HW-Lab-Hardware-Design-Agency/WebScreen-PCB/kicad_project/3Dlib/MicroSD_Socket.STEP

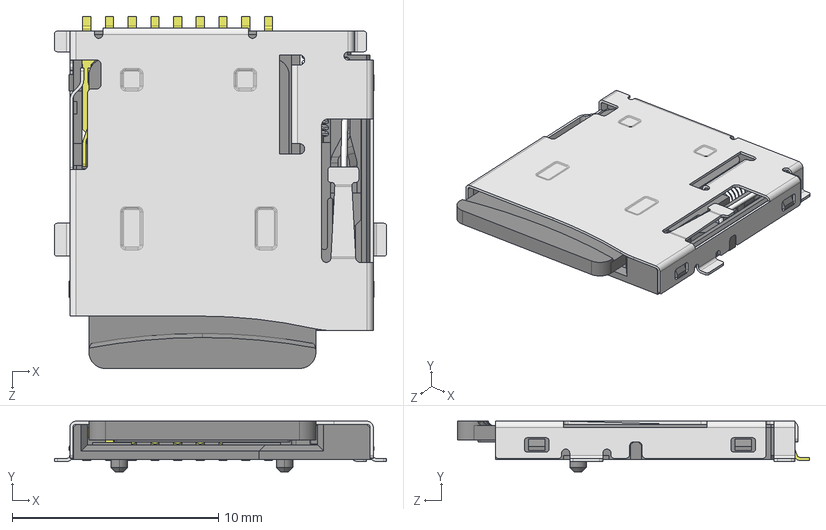
[picture p17: CAD file, 2024-11-25]
kicad_project/3Dlib/MicroSD_Socket.STEP
16.1 x 2.45 x 17.0 mm
Case^MicroSD_Socket
Insert^MicroSD_Socket
Brace^MicroSD_Socket
Spring^MicroSD_Socket
Lid^MicroSD_Socket
Pin_Middle^MicroSD_Socket x 5
Pin_Short^MicroSD_Socket
Pin_Long^MicroSD_Socket x 2
MicroSD_Card^MicroSD_Socket
Pin_CardIn^MicroSD_Socket
