HW-Lab-Hardware-Design-Agency/WebScreen-PCB/kicad_project/3Dlib/33FXRH-SM1-GAN-TF.STEP

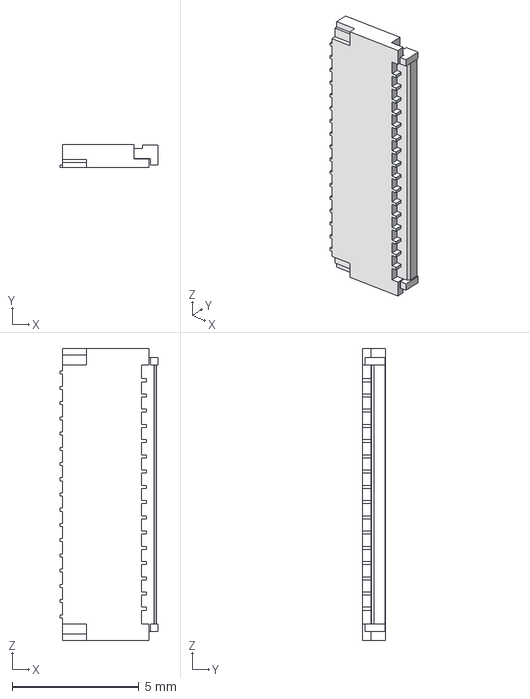
[picture p18: CAD file, 2024-11-25]
kicad_project/3Dlib/33FXRH-SM1-GAN-TF.STEP
3.85 x 0.9 x 11.5 mm
