HW-Lab-Hardware-Design-Agency/WebScreen-PCB/kicad_project/3Dlib/L_0201_0603Metric.step

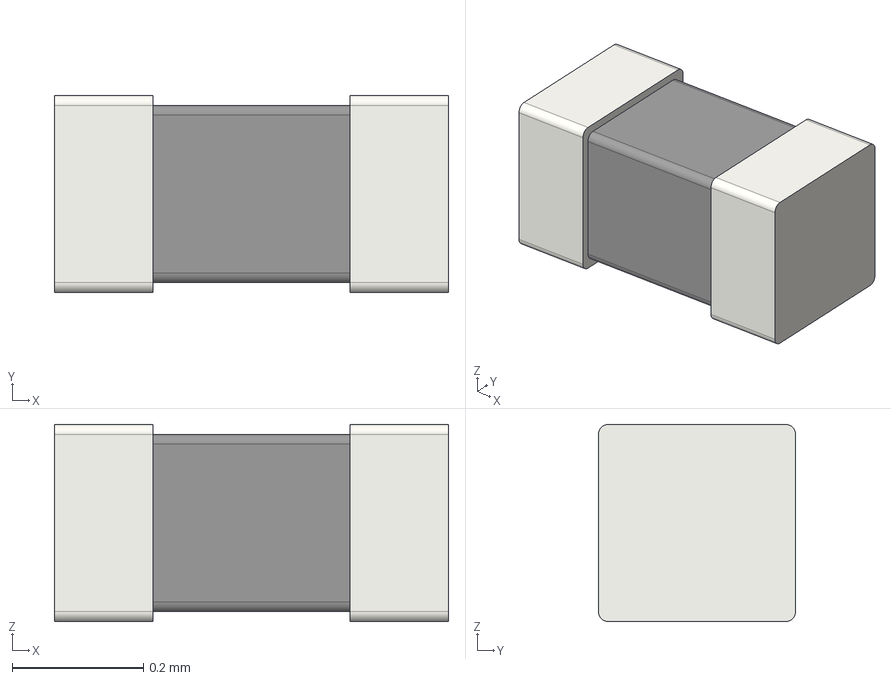
[picture p19: CAD file, 2024-11-25]
kicad_project/3Dlib/L_0201_0603Metric.step
0.6 x 0.3 x 0.3 mm
