HW-Lab-Hardware-Design-Agency/WebScreen-PCB/kicad_project/3Dlib/USB_C_HC019-1E1H1A103-0HR.step

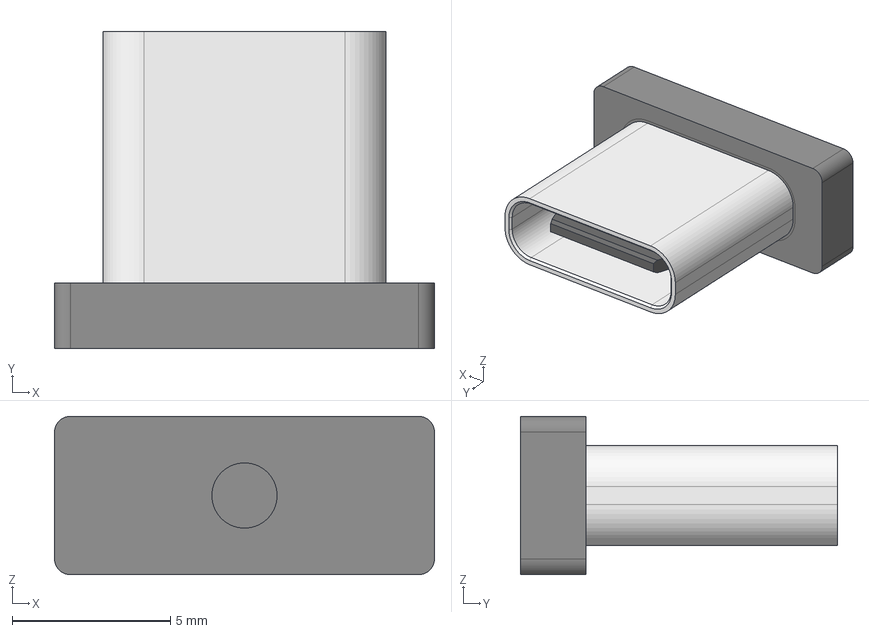
[picture p20: CAD file, 2024-11-25]
kicad_project/3Dlib/USB_C_HC019-1E1H1A103-0HR.step
12.0 x 10.0 x 5.00 mm
