HW-Lab-Hardware-Design-Agency/WebScreen-PCB/kicad_project/3Dlib/r_0402_h040.step

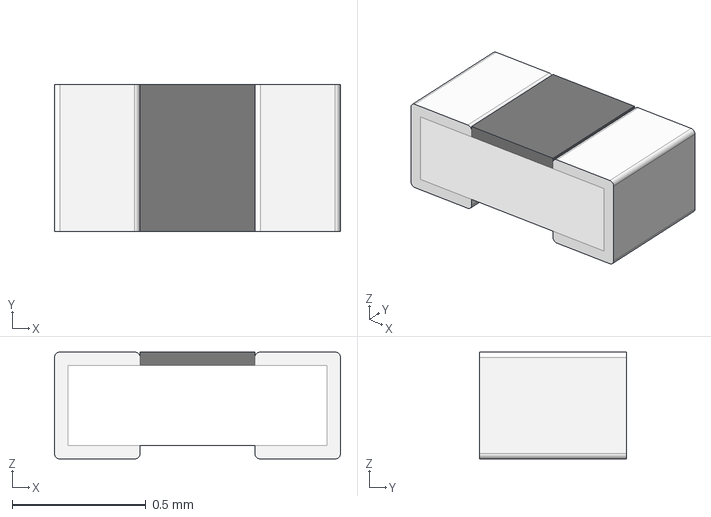
[picture p21: CAD file, 2024-11-25]
kicad_project/3Dlib/r_0402_h040.step
1.07 x 0.55 x 0.4 mm
