HW-Lab-Hardware-Design-Agency/WebScreen-PCB/kicad_project/3Dlib/c_1206_h160.step

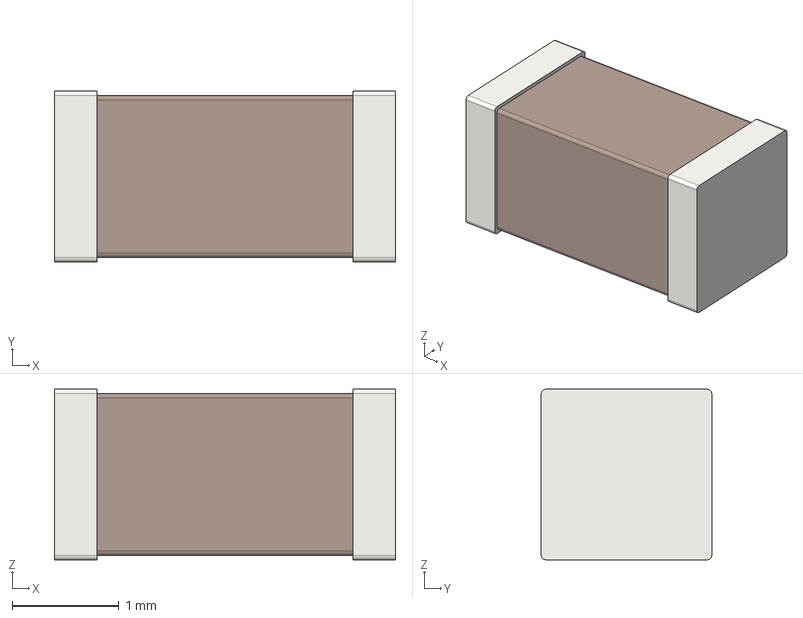
[picture p22: CAD file, 2024-11-25]
kicad_project/3Dlib/c_1206_h160.step
3.20 x 1.60 x 1.60 mm
