HW-Lab-Hardware-Design-Agency/WebScreen-PCB/kicad_project/3Dlib/AXPM65611.step

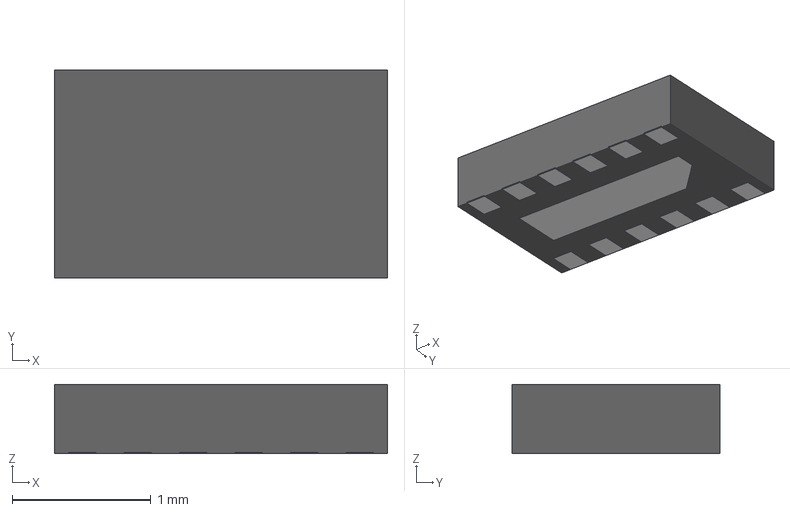
[picture p23: CAD file, 2024-11-25]
kicad_project/3Dlib/AXPM65611.step
2.40 x 1.50 x 0.5 mm
main_Body001
mainPad001
