HW-Lab-Hardware-Design-Agency/WebScreen-PCB/kicad_project/3Dlib/c_1210.step

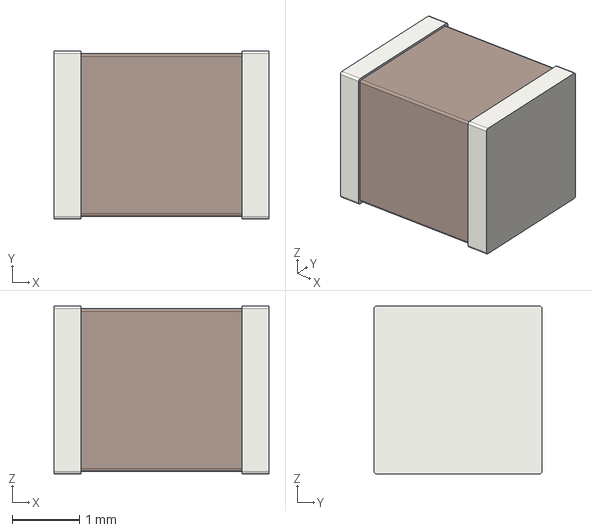
[picture p24: CAD file, 2024-11-25]
kicad_project/3Dlib/c_1210.step
3.20 x 2.50 x 2.50 mm
