HW-Lab-Hardware-Design-Agency/WebScreen-PCB/kicad_project/3Dlib/SY8089A1AAC.stp

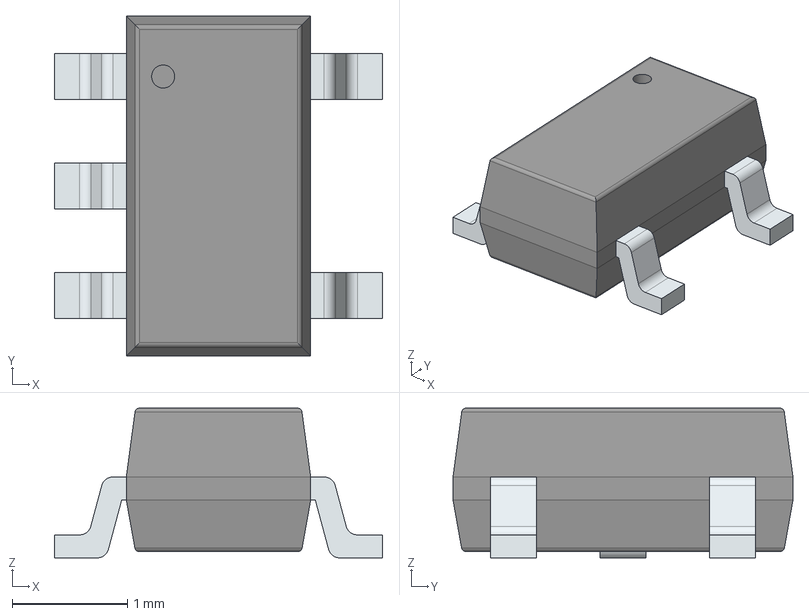
[picture p25: CAD file, 2024-11-25]
kicad_project/3Dlib/SY8089A1AAC.stp
2.85 x 2.95 x 1.30 mm
PinsArrayL
PinsArrayR
