HW-Lab-Hardware-Design-Agency/WebScreen-PCB/kicad_project/3Dlib/C_0402_1005Metric.step

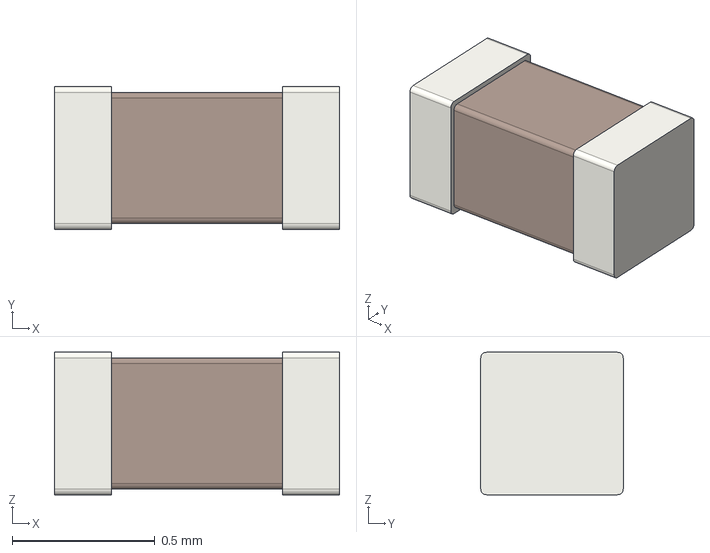
[picture p26: CAD file, 2024-11-25]
kicad_project/3Dlib/C_0402_1005Metric.step
1.00 x 0.5 x 0.5 mm
