HW-Lab-Hardware-Design-Agency/WebScreen-PCB/kicad_project/3Dlib/BRFL2518T1R0M.STEP

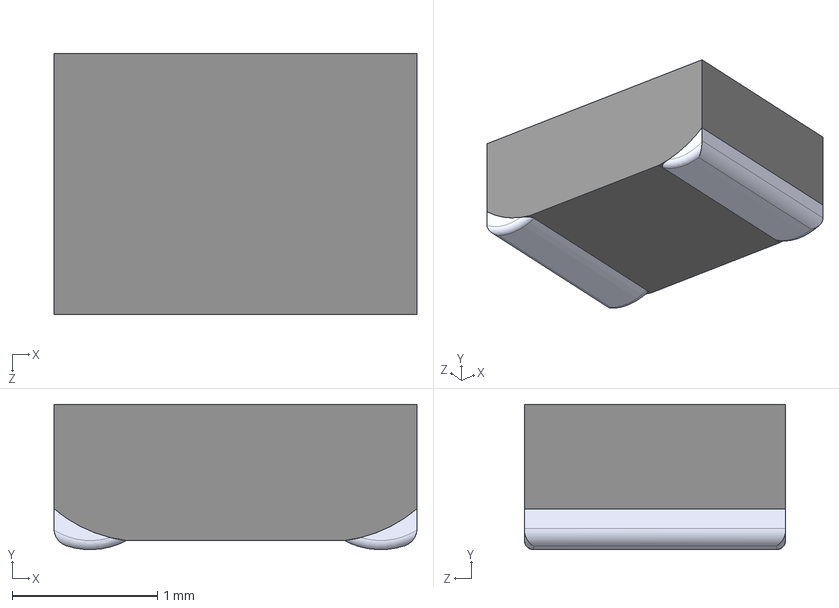
[picture p27: CAD file, 2024-11-25]
kicad_project/3Dlib/BRFL2518T1R0M.STEP
2.50 x 1 x 1.80 mm
