HW-Lab-Hardware-Design-Agency/WebScreen-PCB/kicad_project/3Dlib/led_0603.step

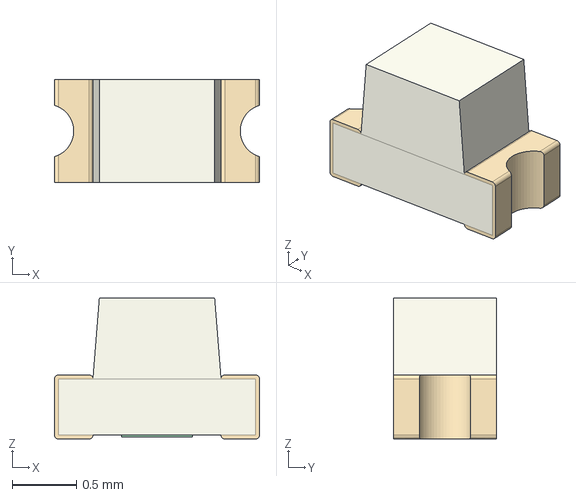
[picture p28: CAD file, 2024-11-25]
kicad_project/3Dlib/led_0603.step
1.60 x 0.8 x 1.10 mm
