HW-Lab-Hardware-Design-Agency/WebScreen-PCB/kicad_project/3Dlib/Crystal_SMD_3225-4Pin_3.2x2.5mm.step

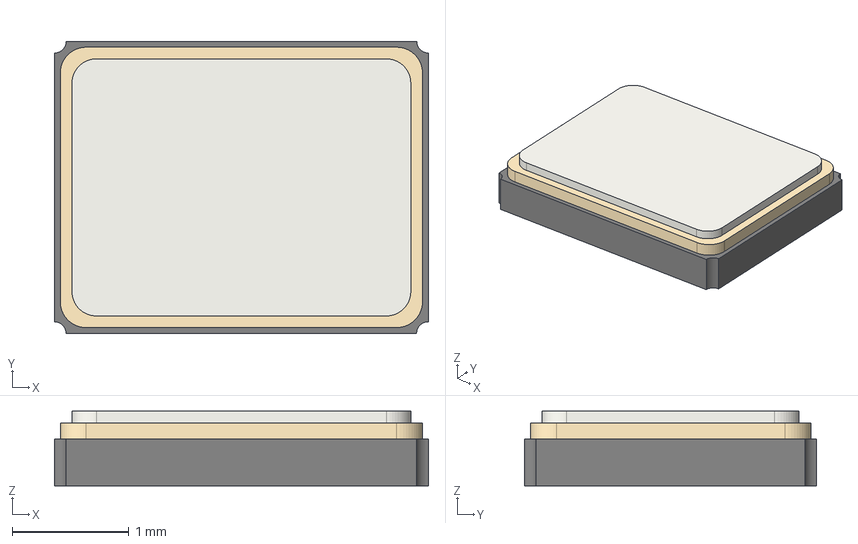
[picture p29: CAD file, 2024-11-25]
kicad_project/3Dlib/Crystal_SMD_3225-4Pin_3.2x2.5mm.step
3.20 x 2.50 x 0.64 mm
