HW-Lab-Hardware-Design-Agency/WebScreen-PCB/kicad_project/3Dlib/ESP32-S3R8.stp

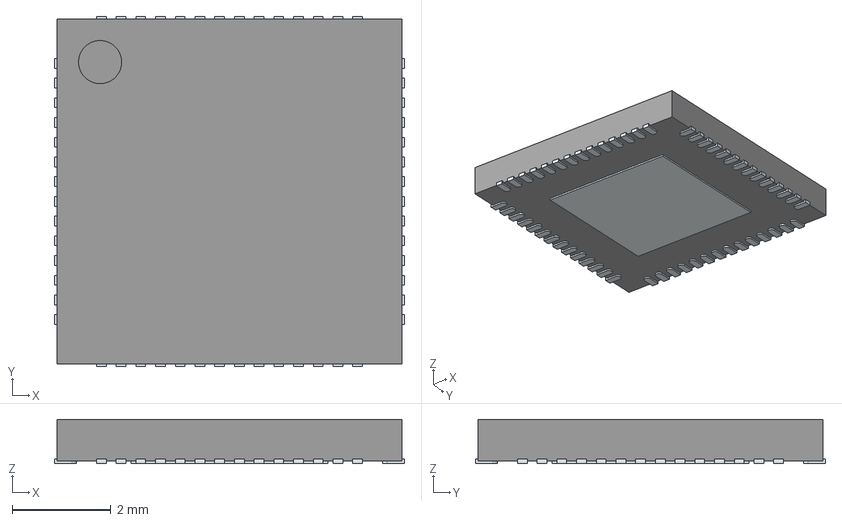
[picture p30: CAD file, 2024-11-25]
kicad_project/3Dlib/ESP32-S3R8.stp
7.10 x 7.10 x 0.9 mm
ThermalPin
PinsArrayLR
PinsArrayTB
